FarmingSoul/Chariot_manute/media/IMG_20201209_215819.jpg

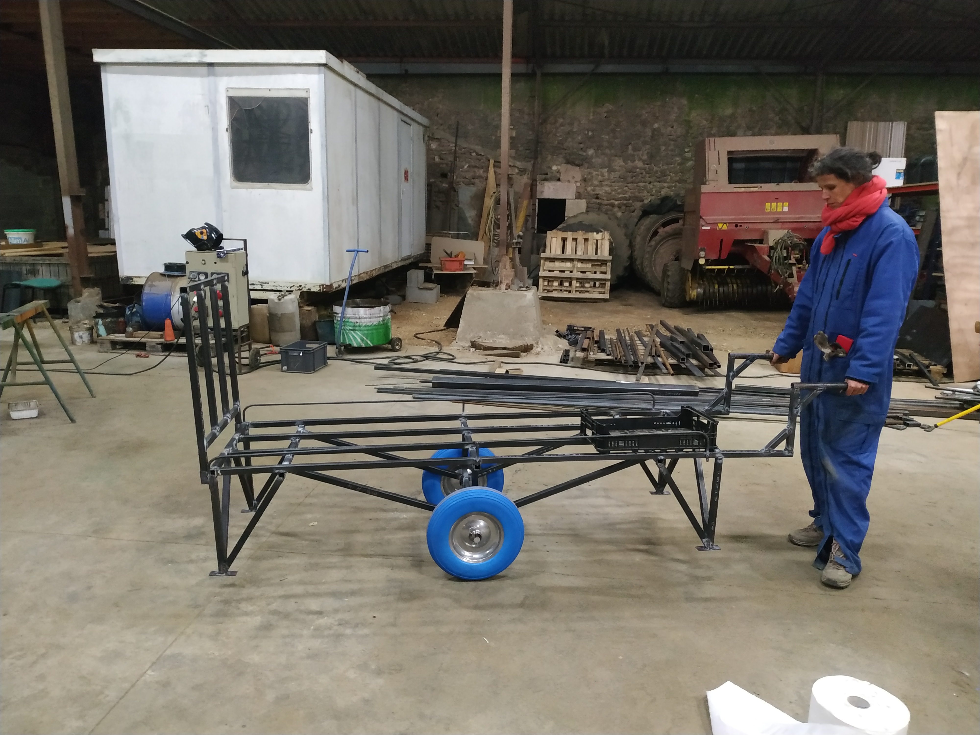
media/IMG_20201209_215819.jpg
