FarmingSoul/Chariot_manute/plans/5.pdf

195 mm

01/03/25 | 5/16

Nomenclature complète; Brouette Balance; B - Nomenclature
