FarmingSoul/Chariot_manute/plans/6.pdf

A | A8

1

Brouette Balance; pas a pas etape 1

Souder les pièces du plateau

principal de la brouette
