FarmingSoul/Chariot_manute/plans/7.pdf

01/03/25 | 7/16

brouette à l'envers; Brouette Balance; pas a pas etape 2

souder les 3 A2 restantes
