FarmingSoul/Chariot_manute/plans/9.pdf

01/03/25 | 9/16

à l'étape précédente; Brouette Balance; pas a pas etape 4

placer les renforts des pièces installées
